DeltaLabo/rsim/tests/mac_address/mac_address.ino

// Complete Instructions to Get and Change ESP MAC Address: https://RandomNerdTutorials.com/get-change-esp32-esp8266-mac-address-arduino/

// XIAO: 48:27:E2:E6:DC:84
// DevKit: C0:4E:30:3A:03:34

#include "WiFi.h"
 
void setup(){
  Serial.begin(115200);
  WiFi.mode(WIFI_MODE_STA);
  Serial.println(WiFi.macAddress());
}
 
void loop(){

}
